XIGUAjuice/MyHoloCubic/Simulator/base_face.png

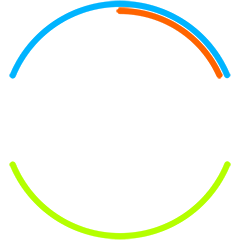
Simulator/base_face.png
