XIGUAjuice/MyHoloCubic/Simulator/smart_config.png

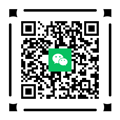
Simulator/smart_config.png
