XIGUAjuice/MyHoloCubic/Sources/pngs/1baitianqing.png

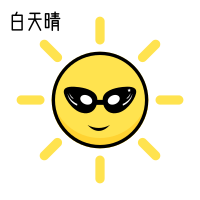
Sources/pngs/1baitianqing.png
