XIGUAjuice/MyHoloCubic/Sources/pngs/2yejianqing.png

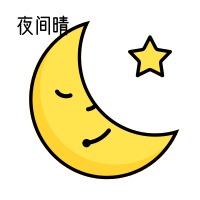
Sources/pngs/2yejianqing.png
