XIGUAjuice/MyHoloCubic/Sources/pngs/3qingtianduoyun.png

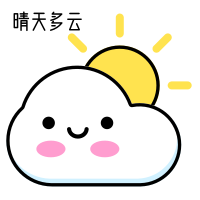
Sources/pngs/3qingtianduoyun.png
