XIGUAjuice/MyHoloCubic/Sources/pngs/4yewanduoyun.png

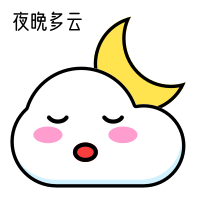
Sources/pngs/4yewanduoyun.png
