XIGUAjuice/MyHoloCubic/Sources/pngs/5yin.png

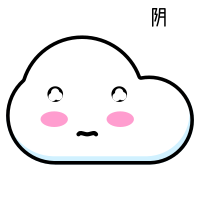
Sources/pngs/5yin.png
