XIGUAjuice/MyHoloCubic/Sources/pngs/6baitianzhenyu.png

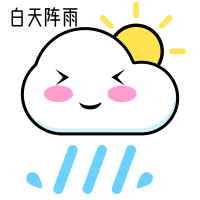
Sources/pngs/6baitianzhenyu.png
