XIGUAjuice/MyHoloCubic/Sources/pngs/7yewanzhenyu.png

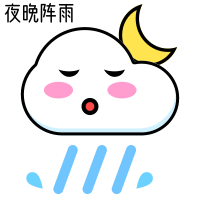
Sources/pngs/7yewanzhenyu.png
