XIGUAjuice/MyHoloCubic/Sources/pngs/10yujiaxue.png

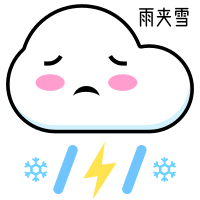
Sources/pngs/10yujiaxue.png
