XIGUAjuice/MyHoloCubic/Sources/pngs/11xiaoyu.png

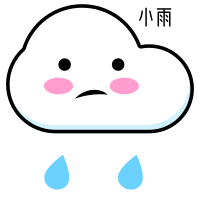
Sources/pngs/11xiaoyu.png
