XIGUAjuice/MyHoloCubic/Sources/pngs/12zhongyu.png

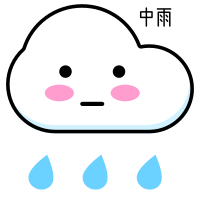
Sources/pngs/12zhongyu.png
