XIGUAjuice/MyHoloCubic/Sources/pngs/15dabaoyu.png

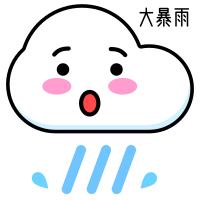
Sources/pngs/15dabaoyu.png
