XIGUAjuice/MyHoloCubic/Sources/pngs/16tedabaoyu.png

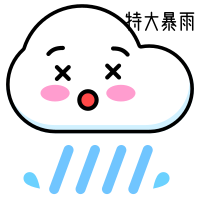
Sources/pngs/16tedabaoyu.png
