XIGUAjuice/MyHoloCubic/Sources/pngs/17qingtianzhenxue.png

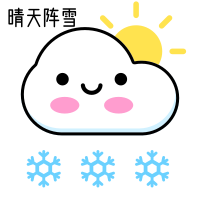
Sources/pngs/17qingtianzhenxue.png
