XIGUAjuice/MyHoloCubic/Sources/pngs/18yejianzhenxue.png

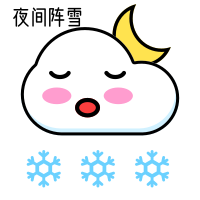
Sources/pngs/18yejianzhenxue.png
