XIGUAjuice/MyHoloCubic/Sources/pngs/19xiaoxue.png

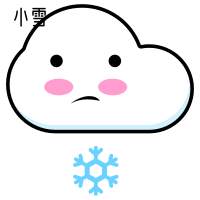
Sources/pngs/19xiaoxue.png
