XIGUAjuice/MyHoloCubic/Sources/pngs/20zhongxue.png

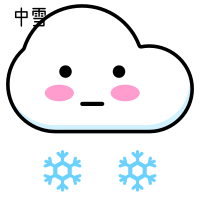
Sources/pngs/20zhongxue.png
