XIGUAjuice/MyHoloCubic/Sources/pngs/21daxue.png

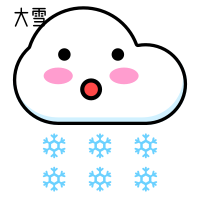
Sources/pngs/21daxue.png
