XIGUAjuice/MyHoloCubic/Sources/pngs/22baoxue.png

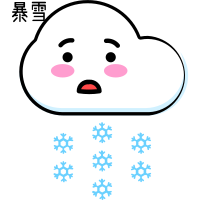
Sources/pngs/22baoxue.png
