XIGUAjuice/MyHoloCubic/Sources/pngs/24yejianwu.png

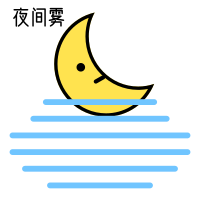
Sources/pngs/24yejianwu.png
