XIGUAjuice/MyHoloCubic/Sources/pngs/29wumai.png

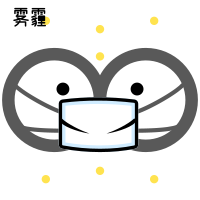
Sources/pngs/29wumai.png
