XIGUAjuice/MyHoloCubic/Sources/pngs/31reqiwengao.png

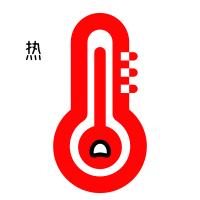
Sources/pngs/31reqiwengao.png
