XIGUAjuice/MyHoloCubic/Sources/pngs/32lengqiwendi.png

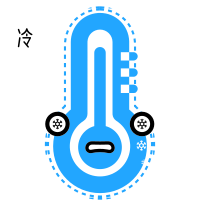
Sources/pngs/32lengqiwendi.png
