XIGUAjuice/MyHoloCubic/Sources/pngs_small_size/smart_config.png

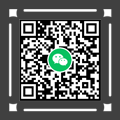
Sources/pngs_small_size/smart_config.png
