XIGUAjuice/MyHoloCubic/Simulator/png_decoder_test.c

#include "lvgl.h"

const uint8_t png_decoder_test_map[] = {
  0x89, 0x50, 0x4e, 0x47, 0x0d, 0x0a, 0x1a, 0x0a, 0x00, 0x00, 0x00, 0x0d, 0x49, 0x48, 0x44, 0x52,
  0x00, 0x00, 0x00, 0xc8, 0x00, 0x00, 0x00, 0x96, 0x08, 0x06, 0x00, 0x00, 0x00, 0x9b, 0xdc, 0xc7,
  0x19, 0x00, 0x00, 0x00, 0x06, 0x62, 0x4b, 0x47, 0x44, 0x00, 0xff, 0x00, 0xff, 0x00, 0xff, 0xa0,
  0xbd, 0xa7, 0x93, 0x00, 0x00, 0x00, 0x09, 0x70, 0x48, 0x59, 0x73, 0x00, 0x00, 0x0b, 0x13, 0x00,
  0x00, 0x0b, 0x13, 0x01, 0x00, 0x9a, 0x9c, 0x18, 0x00, 0x00, 0x00, 0x07, 0x74, 0x49, 0x4d, 0x45,
  0x07, 0xe2, 0x08, 0x1a, 0x12, 0x00, 0x07, 0x19, 0x4a, 0x0e, 0xae, 0x00, 0x00, 0x00, 0x1d, 0x69,
  0x54, 0x58, 0x74, 0x43, 0x6f, 0x6d, 0x6d, 0x65, 0x6e, 0x74, 0x00, 0x00, 0x00, 0x00, 0x00, 0x43,
  0x72, 0x65, 0x61, 0x74, 0x65, 0x64, 0x20, 0x77, 0x69, 0x74, 0x68, 0x20, 0x47, 0x49, 0x4d, 0x50,
  0x64, 0x2e, 0x65, 0x07, 0x00, 0x00, 0x20, 0x00, 0x49, 0x44, 0x41, 0x54, 0x78, 0xda, 0xec, 0xdd,
  0x79, 0xb4, 0xe5, 0xd7, 0x75, 0x17, 0xf8, 0xcf, 0xf9, 0x0d, 0x77, 0x7c, 0x53, 0xbd, 0x7a, 0x35,
  0x97, 0xa4, 0x2a, 0x95, 0x54, 0x9a, 0x6c, 0x79, 0x90, 0x12, 0xcb, 0x53, 0x8c, 0x1d, 0x03, 0x26,
  0x09, 0x26, 0x03, 0xa4, 0x93, 0x95, 0x0e, 0x43, 0x08, 0xd0, 0x9d, 0xa4, 0xd3, 0x84, 0xb1, 0x59,
  0xc0, 0x6a, 0xd6, 0xea, 0xd0, 0x8b, 0x0c, 0x74, 0x08, 0x1d, 0x12, 0x9a, 0x10, 0x02, 0x04, 0x16,
  0x8b, 0xd0, 0xed, 0x0e, 0x24, 0x24, 0x21, 0xc4, 0x4e, 0x82, 0x9d, 0x78, 0xb6, 0x2c, 0x5b, 0xb2,
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
  0xa0, 0x62, 0x1d, 0xc3, 0x9c, 0x69, 0xc6, 0xac, 0x4b, 0x2f, 0xa7, 0x5d, 0x30, 0xce, 0x92, 0x61,
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
};

lv_img_dsc_t png_decoder_test = {
  .header.always_zero = 0,
  .header.w = 200,
  .header.h = 150,
  .data_size = 20869,
  .header.cf = LV_IMG_CF_RAW_ALPHA,
  .data = png_decoder_test_map,
};
