XIGUAjuice/MyHoloCubic/Simulator/src/alphabet.c

/*******************************************************************************
 * Size: 15 px
 * Bpp: 4
 * Opts: 
 ******************************************************************************/

#ifdef LV_LVGL_H_INCLUDE_SIMPLE
#include "lvgl.h"
#else
#include "lvgl/lvgl.h"
#endif

#ifndef ALPHABET
#define ALPHABET 1
#endif

#if ALPHABET

/*-----------------
 *    BITMAPS
 *----------------*/

/*Store the image of the glyphs*/
static LV_ATTRIBUTE_LARGE_CONST const uint8_t glyph_bitmap[] = {
    /* U+0020 " " */

    /* U+0021 "!" */
    0x4b, 0x4e, 0x6d, 0x6d, 0x7c, 0x7d, 0x9b, 0x7a,
    0x0, 0x29, 0x5b, 0x0,

    /* U+0022 "\"" */
    0x10, 0x0, 0xa7, 0x68, 0xa6, 0x6c, 0x88, 0x8c,
    0x21, 0x45,

    /* U+0023 "#" */
    0x0, 0x0, 0x6b, 0xa, 0x60, 0x0, 0x0, 0xc8,
    0xe, 0x60, 0x0, 0x0, 0xf5, 0x2f, 0x20, 0x2,
    0xbd, 0xfd, 0xef, 0xda, 0x1, 0x6b, 0xd6, 0xcd,
    0x54, 0x0, 0xa, 0x90, 0xb8, 0x0, 0x0, 0xe,
    0x70, 0xea, 0x70, 0x3e, 0xdf, 0xdc, 0xfb, 0xe2,
    0x0, 0x6e, 0x5, 0xf0, 0x0, 0x0, 0x9a, 0x8,
    0xc0, 0x0, 0x0, 0x96, 0x6, 0x80, 0x0,

    /* U+0024 "$" */
    0x0, 0x4, 0xb0, 0x0, 0x0, 0x3c, 0xfa, 0x0,
    0x4, 0xfa, 0x8e, 0xd0, 0xa, 0xa0, 0x3, 0xf1,
    0x7, 0xd0, 0x1, 0xb0, 0x1, 0xdb, 0x10, 0x0,
    0x0, 0x1b, 0xf9, 0x0, 0x4, 0x0, 0x3d, 0xb0,
    0xe, 0x90, 0x5, 0xf0, 0x4, 0xfc, 0x8e, 0xb0,
    0x0, 0xbf, 0xf9, 0x10, 0x0, 0xd, 0x30, 0x0,

    /* U+0025 "%" */
    0x4, 0xef, 0x80, 0x0, 0x0, 0x0, 0xe8, 0x4e,
    0x41, 0xa0, 0x0, 0xf, 0x0, 0x99, 0x6c, 0x0,
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
    0x5, 0x30, 0x0, 0x0,

    /* U+007A "z" */
    0x0, 0x0, 0x0, 0x82, 0xb, 0xbb, 0xbe, 0xc2,
    0x0, 0x0, 0x5c, 0x10, 0x0, 0x6, 0xe1, 0x0,
    0x0, 0x4f, 0x40, 0x0, 0x3, 0xf6, 0x0, 0x0,
    0xe, 0xc5, 0x54, 0x40, 0x5f, 0xff, 0xff, 0xe2,
    0x0, 0x0, 0x0, 0x0,

    /* U+007B "{" */
    0x0, 0x1d, 0x30, 0x8, 0xc0, 0x1, 0xf3, 0x0,
    0x3f, 0x0, 0x4, 0xc0, 0x2, 0xd8, 0x0, 0x6f,
    0x40, 0x0, 0x7c, 0x0, 0x1, 0xf1, 0x0, 0xd,
    0x40, 0x0, 0x99, 0x0, 0x2, 0xe9, 0x0, 0x0,
    0x0,

    /* U+007C "|" */
    0x1e, 0x1, 0xf2, 0x2f, 0x13, 0xf1, 0x4f, 0x14,
    0xf0, 0x4f, 0x5, 0xf0, 0x5f, 0x4, 0xf0, 0x4f,
    0x5, 0xe0, 0x5e, 0x0, 0x30,

    /* U+007D "}" */
    0xbc, 0x10, 0x0, 0xbb, 0x0, 0x2, 0xf0, 0x0,
    0xf, 0x10, 0x0, 0xc5, 0x0, 0x7, 0xe4, 0x0,
    0x4f, 0x70, 0xc, 0x80, 0x1, 0xf2, 0x0, 0x3e,
    0x0, 0x9, 0x90, 0x9, 0xd2, 0x0, 0x0, 0x0,
    0x0,

    /* U+007E "~" */
    0x0, 0x0, 0x0, 0x0, 0x0, 0x2, 0xff, 0xf6,
    0x5, 0xf0, 0xc, 0xa3, 0x6e, 0xef, 0x70, 0x3,
    0x0, 0x0, 0x31, 0x0
};


/*---------------------
 *  GLYPH DESCRIPTION
 *--------------------*/

static const lv_font_fmt_txt_glyph_dsc_t glyph_dsc[] = {
    {.bitmap_index = 0, .adv_w = 0, .box_w = 0, .box_h = 0, .ofs_x = 0, .ofs_y = 0} /* id = 0 reserved */,
    {.bitmap_index = 0, .adv_w = 52, .box_w = 0, .box_h = 0, .ofs_x = 0, .ofs_y = 0},
    {.bitmap_index = 0, .adv_w = 69, .box_w = 2, .box_h = 12, .ofs_x = 1, .ofs_y = -1},
    {.bitmap_index = 12, .adv_w = 97, .box_w = 4, .box_h = 5, .ofs_x = 1, .ofs_y = 7},
    {.bitmap_index = 22, .adv_w = 150, .box_w = 10, .box_h = 11, .ofs_x = -1, .ofs_y = 0},
    {.bitmap_index = 77, .adv_w = 130, .box_w = 8, .box_h = 12, .ofs_x = 0, .ofs_y = -1},
    {.bitmap_index = 125, .adv_w = 177, .box_w = 11, .box_h = 12, .ofs_x = 0, .ofs_y = -1},
    {.bitmap_index = 191, .adv_w = 150, .box_w = 9, .box_h = 11, .ofs_x = 0, .ofs_y = 0},
    {.bitmap_index = 241, .adv_w = 48, .box_w = 3, .box_h = 4, .ofs_x = 0, .ofs_y = 7},
    {.bitmap_index = 247, .adv_w = 80, .box_w = 4, .box_h = 14, .ofs_x = 1, .ofs_y = -3},
    {.bitmap_index = 275, .adv_w = 81, .box_w = 5, .box_h = 14, .ofs_x = -1, .ofs_y = -3},
    {.bitmap_index = 310, .adv_w = 111, .box_w = 7, .box_h = 6, .ofs_x = 0, .ofs_y = 5},
    {.bitmap_index = 331, .adv_w = 136, .box_w = 10, .box_h = 9, .ofs_x = -1, .ofs_y = 0},
    {.bitmap_index = 376, .adv_w = 61, .box_w = 3, .box_h = 4, .ofs_x = 0, .ofs_y = -2},
    {.bitmap_index = 382, .adv_w = 102, .box_w = 6, .box_h = 3, .ofs_x = 0, .ofs_y = 3},
    {.bitmap_index = 391, .adv_w = 53, .box_w = 3, .box_h = 2, .ofs_x = 0, .ofs_y = 0},
    {.bitmap_index = 394, .adv_w = 86, .box_w = 5, .box_h = 12, .ofs_x = 0, .ofs_y = -1},
    {.bitmap_index = 424, .adv_w = 164, .box_w = 10, .box_h = 11, .ofs_x = 0, .ofs_y = 0},
    {.bitmap_index = 479, .adv_w = 94, .box_w = 5, .box_h = 11, .ofs_x = 0, .ofs_y = 0},
    {.bitmap_index = 507, .adv_w = 134, .box_w = 8, .box_h = 12, .ofs_x = 0, .ofs_y = -1},
    {.bitmap_index = 555, .adv_w = 134, .box_w = 8, .box_h = 11, .ofs_x = 0, .ofs_y = 0},
    {.bitmap_index = 599, .adv_w = 139, .box_w = 9, .box_h = 11, .ofs_x = 0, .ofs_y = 0},
    {.bitmap_index = 649, .adv_w = 130, .box_w = 8, .box_h = 11, .ofs_x = 0, .ofs_y = 0},
    {.bitmap_index = 693, .adv_w = 140, .box_w = 8, .box_h = 12, .ofs_x = 0, .ofs_y = 0},
    {.bitmap_index = 741, .adv_w = 127, .box_w = 8, .box_h = 11, .ofs_x = 0, .ofs_y = 0},
    {.bitmap_index = 785, .adv_w = 121, .box_w = 8, .box_h = 13, .ofs_x = 0, .ofs_y = -1},
    {.bitmap_index = 837, .adv_w = 124, .box_w = 7, .box_h = 11, .ofs_x = 0, .ofs_y = 0},
    {.bitmap_index = 876, .adv_w = 64, .box_w = 3, .box_h = 7, .ofs_x = 0, .ofs_y = 0},
    {.bitmap_index = 887, .adv_w = 67, .box_w = 3, .box_h = 8, .ofs_x = 0, .ofs_y = -1},
    {.bitmap_index = 899, .adv_w = 136, .box_w = 8, .box_h = 8, .ofs_x = 0, .ofs_y = 0},
    {.bitmap_index = 931, .adv_w = 143, .box_w = 7, .box_h = 6, .ofs_x = 1, .ofs_y = 1},
    {.bitmap_index = 952, .adv_w = 131, .box_w = 8, .box_h = 7, .ofs_x = 0, .ofs_y = 1},
    {.bitmap_index = 980, .adv_w = 106, .box_w = 6, .box_h = 11, .ofs_x = 0, .ofs_y = 0},
    {.bitmap_index = 1013, .adv_w = 191, .box_w = 11, .box_h = 13, .ofs_x = 0, .ofs_y = -2},
    {.bitmap_index = 1085, .adv_w = 156, .box_w = 10, .box_h = 11, .ofs_x = 0, .ofs_y = 0},
    {.bitmap_index = 1140, .adv_w = 136, .box_w = 8, .box_h = 11, .ofs_x = 0, .ofs_y = 0},
    {.bitmap_index = 1184, .adv_w = 148, .box_w = 9, .box_h = 13, .ofs_x = 0, .ofs_y = -1},
    {.bitmap_index = 1243, .adv_w = 150, .box_w = 8, .box_h = 11, .ofs_x = 1, .ofs_y = 0},
    {.bitmap_index = 1287, .adv_w = 125, .box_w = 8, .box_h = 11, .ofs_x = 0, .ofs_y = 0},
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
    {.bitmap_index = 3143, .adv_w = 121, .box_w = 7, .box_h = 9, .ofs_x = 0, .ofs_y = -1},
    {.bitmap_index = 3175, .adv_w = 108, .box_w = 8, .box_h = 8, .ofs_x = -1, .ofs_y = 0},
    {.bitmap_index = 3207, .adv_w = 162, .box_w = 10, .box_h = 8, .ofs_x = 0, .ofs_y = 0},
    {.bitmap_index = 3247, .adv_w = 120, .box_w = 7, .box_h = 8, .ofs_x = 0, .ofs_y = 0},
    {.bitmap_index = 3275, .adv_w = 102, .box_w = 8, .box_h = 11, .ofs_x = -1, .ofs_y = -3},
    {.bitmap_index = 3319, .adv_w = 125, .box_w = 8, .box_h = 9, .ofs_x = 0, .ofs_y = -1},
    {.bitmap_index = 3355, .adv_w = 80, .box_w = 5, .box_h = 13, .ofs_x = 0, .ofs_y = -2},
    {.bitmap_index = 3388, .adv_w = 75, .box_w = 3, .box_h = 14, .ofs_x = 1, .ofs_y = -3},
    {.bitmap_index = 3409, .adv_w = 93, .box_w = 5, .box_h = 13, .ofs_x = 0, .ofs_y = -2},
    {.bitmap_index = 3442, .adv_w = 157, .box_w = 10, .box_h = 4, .ofs_x = 0, .ofs_y = 3}
};

/*---------------------
 *  CHARACTER MAPPING
 *--------------------*/



/*Collect the unicode lists and glyph_id offsets*/
static const lv_font_fmt_txt_cmap_t cmaps[] =
{
    {
        .range_start = 32, .range_length = 95, .glyph_id_start = 1,
        .unicode_list = NULL, .glyph_id_ofs_list = NULL, .list_length = 0, .type = LV_FONT_FMT_TXT_CMAP_FORMAT0_TINY
    }
};

/*-----------------
 *    KERNING
 *----------------*/


/*Pair left and right glyphs for kerning*/
static const uint8_t kern_pair_glyph_ids[] =
{
    14, 49,
    15, 41,
    15, 46,
    15, 47,
    15, 49,
    15, 51,
    15, 53,
    15, 54,
    15, 55,
    15, 58,
    19, 20,
    23, 24,
    34, 8,
    34, 35,
    34, 53,
    34, 55,
    34, 56,
    34, 78,
    34, 86,
    34, 87,
    34, 88,
    34, 90,
    34, 91,
    36, 37,
    36, 48,
    37, 86,
    38, 47,
    38, 89,
    39, 40,
    39, 66,
    39, 70,
    39, 80,
    40, 41,
    40, 77,
    41, 15,
    41, 70,
    42, 68,
    43, 15,
    45, 53,
    46, 15,
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
};

/* Kerning between the respective left and right glyphs
 * 4.4 format which needs to scaled with `kern_scale`*/
static const int8_t kern_pair_values[] =
{
    -5, -7, -10, -10, -7, -7, -31, -12,
    -29, -14, -7, -2, -18, -7, -19, -31,
    -14, -5, -10, -14, -7, -10, -2, -3,
    -10, -5, 5, -12, -10, -14, -7, -12,
    -5, -2, -7, -10, -1, -12, -19, -7,
    -46, -26, -7, -10, -5, -17, -7, -14,
    -14, -14, -14, -7, -14, -7, -11, -10,
    -7, -12, -7, -7, -7, -7, -7, -7,
    -12, -4, -5, -18, 5, -14, -22, -4,
    -10, -17, -14, -26, -12, -5, -7, -22,
    -7, -14, -12, 5, -7, -5, -5, -10,
    -7, -5, -14, -10, -7, -7, -5, -14,
    -5, 2, -2, -5, 0, -12, -14, -7,
    -2, -5, -10, -14, -17, -14, -10, -7,
    -5, 2, -10, -10, 2, 5, -6, -2,
    7, 5, -5, -10, -14, -10, -3, -7,
    -10, 5, -5, -2, -5, -11, -10, 0,
    -7, -2, 2, -2, -2, -10, -10, 2,
    -10, 7, 19, -17, -14, -7, -5, -5,
    -5, -12, -11, -10, -5, -7, -11, -5,
    -7, -7, -5, -22, -7, -7, -7, -5,
    -5, -7, -2
};

/*Collect the kern pair's data in one place*/
static const lv_font_fmt_txt_kern_pair_t kern_pairs =
{
    .glyph_ids = kern_pair_glyph_ids,
    .values = kern_pair_values,
    .pair_cnt = 171,
    .glyph_ids_size = 0
};

/*--------------------
 *  ALL CUSTOM DATA
 *--------------------*/

#if LV_VERSION_CHECK(8, 0, 0)
/*Store all the custom data of the font*/
static  lv_font_fmt_txt_glyph_cache_t cache;
static const lv_font_fmt_txt_dsc_t font_dsc = {
#else
static lv_font_fmt_txt_dsc_t font_dsc = {
#endif
    .glyph_bitmap = glyph_bitmap,
    .glyph_dsc = glyph_dsc,
    .cmaps = cmaps,
    .kern_dsc = &kern_pairs,
    .kern_scale = 16,
    .cmap_num = 1,
    .bpp = 4,
    .kern_classes = 0,
    .bitmap_format = 0,
#if LV_VERSION_CHECK(8, 0, 0)
    .cache = &cache
#endif
};


/*-----------------
 *  PUBLIC FONT
 *----------------*/

/*Initialize a public general font descriptor*/
#if LV_VERSION_CHECK(8, 0, 0)
const lv_font_t alphabet = {
#else
lv_font_t alphabet = {
#endif
    .get_glyph_dsc = lv_font_get_glyph_dsc_fmt_txt,    /*Function pointer to get glyph's data*/
    .get_glyph_bitmap = lv_font_get_bitmap_fmt_txt,    /*Function pointer to get glyph's bitmap*/
    .line_height = 15,          /*The maximum line height required by the font*/
    .base_line = 3,             /*Baseline measured from the bottom of the line*/
#if !(LVGL_VERSION_MAJOR == 6 && LVGL_VERSION_MINOR == 0)
    .subpx = LV_FONT_SUBPX_NONE,
#endif
#if LV_VERSION_CHECK(7, 4, 0)
    .underline_position = -1,
    .underline_thickness = 1,
#endif
    .dsc = &font_dsc           /*The custom font data. Will be accessed by `get_glyph_bitmap/dsc` */
};



#endif /*#if ALPHABET*/
