XIGUAjuice/MyHoloCubic/Simulator/src/digital.c

/*******************************************************************************
 * Size: 75 px
 * Bpp: 1
 * Opts: 
 ******************************************************************************/

#ifdef LV_LVGL_H_INCLUDE_SIMPLE
#include "lvgl.h"
#else
#include "lvgl/lvgl.h"
#endif

#ifndef DIGITAL
#define DIGITAL 1
#endif

#if DIGITAL

/*-----------------
 *    BITMAPS
 *----------------*/

/*Store the image of the glyphs*/
static LV_ATTRIBUTE_LARGE_CONST const uint8_t glyph_bitmap[] = {
    /* U+0020 " " */
    0x0,

    /* U+0021 "!" */
    0x3e, 0x3f, 0x9f, 0xcf, 0xe7, 0xf3, 0xf9, 0xfc,
    0xfe, 0x7f, 0x3f, 0x9f, 0xcf, 0xe7, 0xf3, 0xf9,
    0xfc, 0xfe, 0x7f, 0x3f, 0x9f, 0xcf, 0xe7, 0xf3,
    0xf9, 0xfc, 0xfe, 0x7f, 0x3f, 0x9f, 0xcf, 0xe7,
    0xf3, 0xf9, 0xfc, 0xfe, 0x7f, 0x3f, 0x9f, 0xcf,
    0xe7, 0xf3, 0xf9, 0xfc, 0xfe, 0x7f, 0x3f, 0x9f,
    0xcf, 0xe7, 0xf3, 0xf9, 0xfc, 0xfe, 0x7f, 0x3f,
    0x9f, 0xcf, 0xe7, 0xf3, 0xf9, 0xfc, 0xfe, 0x3e,
    0x0, 0x0, 0x0, 0x1, 0xc1, 0xf1, 0xfd, 0xff,
    0xff, 0xff, 0xdf, 0xc7, 0xc1, 0xc0,

    /* U+0022 "\"" */
    0x70, 0x77, 0xc7, 0xfe, 0x3f, 0xf1, 0xff, 0x8f,
    0xf8, 0x7f, 0xc3, 0xde, 0x1e, 0xf0, 0xf7, 0x83,
    0x9c, 0x1c, 0xe0, 0xe6, 0x6, 0x0,

    /* U+0023 "#" */
    0x0, 0x1, 0xf0, 0x0, 0xf8, 0x0, 0x0, 0x7f,
    0x0, 0x3f, 0x80, 0x0, 0xf, 0xe0, 0xf, 0xf0,
    0x0, 0x1, 0xfc, 0x1, 0xfe, 0x0, 0x0, 0x7f,
    0x80, 0x3f, 0xc0, 0x0, 0xf, 0xf0, 0x7, 0xf8,
    0x0, 0x1, 0xfe, 0x0, 0xfe, 0x0, 0x0, 0x3f,
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
    0x1, 0xfc, 0x0, 0xfe, 0x0, 0x7f, 0x0, 0x3f,
    0x80, 0x1f, 0xc0, 0xf, 0xe0, 0x7, 0xf0, 0x3,
    0xf8, 0x1, 0xfc, 0x0, 0xfe, 0x0, 0xff, 0x0,
    0x7f, 0x0, 0x7f, 0x80, 0x7f, 0x80, 0x7f, 0x80,
    0x7f, 0x80, 0x3f, 0x80, 0x3f, 0xc0, 0x1f, 0xc0,
    0x7, 0xc0, 0x0,

    /* U+007E "~" */
    0x3, 0xc0, 0x0, 0x0, 0xfe, 0x0, 0x0, 0x1f,
    0xf8, 0x0, 0x7, 0xff, 0xc0, 0x0, 0xff, 0xff,
    0x0, 0x6f, 0xff, 0xf8, 0x1f, 0xff, 0xff, 0xe3,
    0xff, 0xff, 0xff, 0xff, 0xfc, 0x7f, 0xff, 0xff,
    0x1, 0xff, 0xff, 0x60, 0xf, 0xff, 0xe0, 0x0,
    0x3f, 0xfe, 0x0, 0x1, 0xff, 0x80, 0x0, 0x7,
    0xf0, 0x0, 0x0, 0x3c, 0x0
};


/*---------------------
 *  GLYPH DESCRIPTION
 *--------------------*/

static const lv_font_fmt_txt_glyph_dsc_t glyph_dsc[] = {
    {.bitmap_index = 0, .adv_w = 0, .box_w = 0, .box_h = 0, .ofs_x = 0, .ofs_y = 0} /* id = 0 reserved */,
    {.bitmap_index = 0, .adv_w = 216, .box_w = 1, .box_h = 1, .ofs_x = 0, .ofs_y = 0},
    {.bitmap_index = 1, .adv_w = 235, .box_w = 9, .box_h = 69, .ofs_x = 3, .ofs_y = -8},
    {.bitmap_index = 79, .adv_w = 260, .box_w = 13, .box_h = 13, .ofs_x = 2, .ofs_y = 45},
    {.bitmap_index = 101, .adv_w = 709, .box_w = 43, .box_h = 69, .ofs_x = 2, .ofs_y = -7},
    {.bitmap_index = 472, .adv_w = 595, .box_w = 31, .box_h = 69, .ofs_x = 4, .ofs_y = -7},
    {.bitmap_index = 740, .adv_w = 616, .box_w = 33, .box_h = 69, .ofs_x = 1, .ofs_y = -7},
    {.bitmap_index = 1025, .adv_w = 587, .box_w = 31, .box_h = 69, .ofs_x = 4, .ofs_y = -7},
    {.bitmap_index = 1293, .adv_w = 128, .box_w = 6, .box_h = 13, .ofs_x = 1, .ofs_y = 45},
    {.bitmap_index = 1303, .adv_w = 367, .box_w = 16, .box_h = 69, .ofs_x = 4, .ofs_y = -7},
    {.bitmap_index = 1441, .adv_w = 368, .box_w = 15, .box_h = 69, .ofs_x = 3, .ofs_y = -7},
    {.bitmap_index = 1571, .adv_w = 497, .box_w = 28, .box_h = 33, .ofs_x = 1, .ofs_y = 13},
    {.bitmap_index = 1687, .adv_w = 766, .box_w = 42, .box_h = 45, .ofs_x = 3, .ofs_y = 7},
    {.bitmap_index = 1924, .adv_w = 238, .box_w = 9, .box_h = 15, .ofs_x = 3, .ofs_y = -7},
    {.bitmap_index = 1941, .adv_w = 390, .box_w = 20, .box_h = 7, .ofs_x = 2, .ofs_y = 22},
    {.bitmap_index = 1959, .adv_w = 217, .box_w = 7, .box_h = 9, .ofs_x = 3, .ofs_y = -7},
    {.bitmap_index = 1967, .adv_w = 398, .box_w = 19, .box_h = 69, .ofs_x = 4, .ofs_y = -7},
    {.bitmap_index = 2131, .adv_w = 610, .box_w = 31, .box_h = 55, .ofs_x = 4, .ofs_y = -1},
    {.bitmap_index = 2345, .adv_w = 317, .box_w = 17, .box_h = 55, .ofs_x = 1, .ofs_y = -1},
    {.bitmap_index = 2462, .adv_w = 608, .box_w = 31, .box_h = 55, .ofs_x = 4, .ofs_y = -1},
    {.bitmap_index = 2676, .adv_w = 598, .box_w = 31, .box_h = 55, .ofs_x = 2, .ofs_y = -1},
    {.bitmap_index = 2890, .adv_w = 599, .box_w = 31, .box_h = 55, .ofs_x = 3, .ofs_y = -1},
    {.bitmap_index = 3104, .adv_w = 610, .box_w = 31, .box_h = 55, .ofs_x = 4, .ofs_y = -1},
    {.bitmap_index = 3318, .adv_w = 610, .box_w = 31, .box_h = 55, .ofs_x = 4, .ofs_y = -1},
    {.bitmap_index = 3532, .adv_w = 461, .box_w = 28, .box_h = 55, .ofs_x = -3, .ofs_y = -1},
    {.bitmap_index = 3725, .adv_w = 611, .box_w = 31, .box_h = 55, .ofs_x = 4, .ofs_y = -1},
    {.bitmap_index = 3939, .adv_w = 610, .box_w = 31, .box_h = 55, .ofs_x = 4, .ofs_y = -1},
    {.bitmap_index = 4153, .adv_w = 217, .box_w = 7, .box_h = 37, .ofs_x = 3, .ofs_y = 11},
    {.bitmap_index = 4186, .adv_w = 286, .box_w = 9, .box_h = 44, .ofs_x = 4, .ofs_y = 4},
    {.bitmap_index = 4236, .adv_w = 667, .box_w = 36, .box_h = 65, .ofs_x = 3, .ofs_y = -6},
    {.bitmap_index = 4529, .adv_w = 766, .box_w = 42, .box_h = 28, .ofs_x = 3, .ofs_y = 17},
    {.bitmap_index = 4676, .adv_w = 668, .box_w = 36, .box_h = 65, .ofs_x = 3, .ofs_y = -6},
    {.bitmap_index = 4969, .adv_w = 412, .box_w = 26, .box_h = 62, .ofs_x = -1, .ofs_y = -1},
    {.bitmap_index = 5171, .adv_w = 817, .box_w = 44, .box_h = 55, .ofs_x = 4, .ofs_y = -1},
    {.bitmap_index = 5474, .adv_w = 637, .box_w = 35, .box_h = 55, .ofs_x = 2, .ofs_y = -1},
    {.bitmap_index = 5715, .adv_w = 594, .box_w = 30, .box_h = 55, .ofs_x = 4, .ofs_y = -1},
    {.bitmap_index = 5922, .adv_w = 595, .box_w = 30, .box_h = 55, .ofs_x = 4, .ofs_y = -1},
    {.bitmap_index = 6129, .adv_w = 595, .box_w = 30, .box_h = 55, .ofs_x = 4, .ofs_y = -1},
    {.bitmap_index = 6336, .adv_w = 582, .box_w = 30, .box_h = 55, .ofs_x = 4, .ofs_y = -1},
    {.bitmap_index = 6543, .adv_w = 582, .box_w = 30, .box_h = 55, .ofs_x = 4, .ofs_y = -1},
    {.bitmap_index = 6750, .adv_w = 595, .box_w = 30, .box_h = 55, .ofs_x = 4, .ofs_y = -1},
    {.bitmap_index = 6957, .adv_w = 595, .box_w = 30, .box_h = 55, .ofs_x = 4, .ofs_y = -1},
    {.bitmap_index = 7164, .adv_w = 326, .box_w = 17, .box_h = 55, .ofs_x = 1, .ofs_y = -1},
    {.bitmap_index = 7281, .adv_w = 493, .box_w = 23, .box_h = 55, .ofs_x = 4, .ofs_y = -1},
    {.bitmap_index = 7440, .adv_w = 583, .box_w = 30, .box_h = 55, .ofs_x = 4, .ofs_y = -1},
    {.bitmap_index = 7647, .adv_w = 582, .box_w = 30, .box_h = 55, .ofs_x = 4, .ofs_y = -1},
    {.bitmap_index = 7854, .adv_w = 740, .box_w = 39, .box_h = 55, .ofs_x = 4, .ofs_y = -1},
    {.bitmap_index = 8123, .adv_w = 606, .box_w = 30, .box_h = 55, .ofs_x = 4, .ofs_y = -1},
    {.bitmap_index = 8330, .adv_w = 595, .box_w = 30, .box_h = 55, .ofs_x = 4, .ofs_y = -1},
    {.bitmap_index = 8537, .adv_w = 583, .box_w = 30, .box_h = 55, .ofs_x = 4, .ofs_y = -1},
    {.bitmap_index = 8744, .adv_w = 593, .box_w = 30, .box_h = 61, .ofs_x = 4, .ofs_y = -7},
    {.bitmap_index = 8973, .adv_w = 582, .box_w = 30, .box_h = 55, .ofs_x = 4, .ofs_y = -1},
    {.bitmap_index = 9180, .adv_w = 595, .box_w = 30, .box_h = 56, .ofs_x = 4, .ofs_y = -1},
    {.bitmap_index = 9390, .adv_w = 451, .box_w = 30, .box_h = 55, .ofs_x = -1, .ofs_y = -1},
    {.bitmap_index = 9597, .adv_w = 595, .box_w = 30, .box_h = 55, .ofs_x = 4, .ofs_y = -1},
    {.bitmap_index = 9804, .adv_w = 565, .box_w = 35, .box_h = 55, .ofs_x = 0, .ofs_y = -1},
    {.bitmap_index = 10045, .adv_w = 692, .box_w = 41, .box_h = 55, .ofs_x = 1, .ofs_y = -1},
    {.bitmap_index = 10327, .adv_w = 617, .box_w = 33, .box_h = 55, .ofs_x = 3, .ofs_y = -1},
    {.bitmap_index = 10554, .adv_w = 515, .box_w = 34, .box_h = 55, .ofs_x = -1, .ofs_y = -1},
    {.bitmap_index = 10788, .adv_w = 596, .box_w = 30, .box_h = 55, .ofs_x = 4, .ofs_y = -1},
    {.bitmap_index = 10995, .adv_w = 342, .box_w = 17, .box_h = 68, .ofs_x = 4, .ofs_y = -7},
    {.bitmap_index = 11140, .adv_w = 372, .box_w = 18, .box_h = 70, .ofs_x = 1, .ofs_y = -7},
    {.bitmap_index = 11298, .adv_w = 342, .box_w = 17, .box_h = 69, .ofs_x = 0, .ofs_y = -7},
    {.bitmap_index = 11445, .adv_w = 637, .box_w = 34, .box_h = 28, .ofs_x = 3, .ofs_y = 25},
    {.bitmap_index = 11564, .adv_w = 612, .box_w = 34, .box_h = 5, .ofs_x = 2, .ofs_y = 5},
    {.bitmap_index = 11586, .adv_w = 158, .box_w = 10, .box_h = 11, .ofs_x = 0, .ofs_y = 52},
    {.bitmap_index = 11600, .adv_w = 526, .box_w = 25, .box_h = 38, .ofs_x = 4, .ofs_y = -1},
    {.bitmap_index = 11719, .adv_w = 510, .box_w = 24, .box_h = 55, .ofs_x = 4, .ofs_y = -1},
    {.bitmap_index = 11884, .adv_w = 486, .box_w = 25, .box_h = 38, .ofs_x = 4, .ofs_y = -1},
    {.bitmap_index = 12003, .adv_w = 510, .box_w = 24, .box_h = 55, .ofs_x = 4, .ofs_y = -1},
    {.bitmap_index = 12168, .adv_w = 510, .box_w = 24, .box_h = 38, .ofs_x = 4, .ofs_y = -1},
    {.bitmap_index = 12282, .adv_w = 364, .box_w = 19, .box_h = 55, .ofs_x = 2, .ofs_y = -1},
    {.bitmap_index = 12413, .adv_w = 523, .box_w = 25, .box_h = 44, .ofs_x = 4, .ofs_y = -7},
    {.bitmap_index = 12551, .adv_w = 522, .box_w = 24, .box_h = 55, .ofs_x = 4, .ofs_y = -1},
    {.bitmap_index = 12716, .adv_w = 254, .box_w = 7, .box_h = 49, .ofs_x = 4, .ofs_y = -1},
    {.bitmap_index = 12759, .adv_w = 252, .box_w = 12, .box_h = 56, .ofs_x = -1, .ofs_y = -7},
    {.bitmap_index = 12843, .adv_w = 436, .box_w = 23, .box_h = 55, .ofs_x = 4, .ofs_y = -1},
    {.bitmap_index = 13002, .adv_w = 228, .box_w = 7, .box_h = 55, .ofs_x = 4, .ofs_y = -1},
    {.bitmap_index = 13051, .adv_w = 710, .box_w = 36, .box_h = 38, .ofs_x = 4, .ofs_y = -1},
    {.bitmap_index = 13222, .adv_w = 536, .box_w = 25, .box_h = 38, .ofs_x = 4, .ofs_y = -1},
    {.bitmap_index = 13341, .adv_w = 512, .box_w = 25, .box_h = 38, .ofs_x = 4, .ofs_y = -1},
    {.bitmap_index = 13460, .adv_w = 522, .box_w = 24, .box_h = 44, .ofs_x = 4, .ofs_y = -7},
    {.bitmap_index = 13592, .adv_w = 522, .box_w = 24, .box_h = 44, .ofs_x = 4, .ofs_y = -7},
    {.bitmap_index = 13724, .adv_w = 276, .box_w = 12, .box_h = 38, .ofs_x = 4, .ofs_y = -1},
    {.bitmap_index = 13781, .adv_w = 511, .box_w = 25, .box_h = 38, .ofs_x = 4, .ofs_y = -1},
    {.bitmap_index = 13900, .adv_w = 408, .box_w = 22, .box_h = 47, .ofs_x = 2, .ofs_y = -1},
    {.bitmap_index = 14030, .adv_w = 535, .box_w = 25, .box_h = 38, .ofs_x = 4, .ofs_y = -1},
    {.bitmap_index = 14149, .adv_w = 446, .box_w = 23, .box_h = 38, .ofs_x = 2, .ofs_y = -1},
    {.bitmap_index = 14259, .adv_w = 725, .box_w = 41, .box_h = 38, .ofs_x = 2, .ofs_y = -1},
    {.bitmap_index = 14454, .adv_w = 428, .box_w = 25, .box_h = 38, .ofs_x = 1, .ofs_y = -1},
    {.bitmap_index = 14573, .adv_w = 499, .box_w = 25, .box_h = 44, .ofs_x = 3, .ofs_y = -7},
    {.bitmap_index = 14711, .adv_w = 461, .box_w = 24, .box_h = 37, .ofs_x = 2, .ofs_y = 0},
    {.bitmap_index = 14822, .adv_w = 325, .box_w = 17, .box_h = 67, .ofs_x = 3, .ofs_y = -7},
    {.bitmap_index = 14965, .adv_w = 233, .box_w = 7, .box_h = 69, .ofs_x = 4, .ofs_y = -7},
    {.bitmap_index = 15026, .adv_w = 328, .box_w = 17, .box_h = 69, .ofs_x = 1, .ofs_y = -7},
    {.bitmap_index = 15173, .adv_w = 515, .box_w = 28, .box_h = 15, .ofs_x = 2, .ofs_y = 24}
};

/*---------------------
 *  CHARACTER MAPPING
 *--------------------*/



/*Collect the unicode lists and glyph_id offsets*/
static const lv_font_fmt_txt_cmap_t cmaps[] =
{
    {
        .range_start = 32, .range_length = 95, .glyph_id_start = 1,
        .unicode_list = NULL, .glyph_id_ofs_list = NULL, .list_length = 0, .type = LV_FONT_FMT_TXT_CMAP_FORMAT0_TINY
    }
};



/*--------------------
 *  ALL CUSTOM DATA
 *--------------------*/

#if LV_VERSION_CHECK(8, 0, 0)
/*Store all the custom data of the font*/
static  lv_font_fmt_txt_glyph_cache_t cache;
static const lv_font_fmt_txt_dsc_t font_dsc = {
#else
static lv_font_fmt_txt_dsc_t font_dsc = {
#endif
    .glyph_bitmap = glyph_bitmap,
    .glyph_dsc = glyph_dsc,
    .cmaps = cmaps,
    .kern_dsc = NULL,
    .kern_scale = 0,
    .cmap_num = 1,
    .bpp = 1,
    .kern_classes = 0,
    .bitmap_format = 0,
#if LV_VERSION_CHECK(8, 0, 0)
    .cache = &cache
#endif
};


/*-----------------
 *  PUBLIC FONT
 *----------------*/

/*Initialize a public general font descriptor*/
#if LV_VERSION_CHECK(8, 0, 0)
const lv_font_t digital = {
#else
lv_font_t digital = {
#endif
    .get_glyph_dsc = lv_font_get_glyph_dsc_fmt_txt,    /*Function pointer to get glyph's data*/
    .get_glyph_bitmap = lv_font_get_bitmap_fmt_txt,    /*Function pointer to get glyph's bitmap*/
    .line_height = 71,          /*The maximum line height required by the font*/
    .base_line = 8,             /*Baseline measured from the bottom of the line*/
#if !(LVGL_VERSION_MAJOR == 6 && LVGL_VERSION_MINOR == 0)
    .subpx = LV_FONT_SUBPX_NONE,
#endif
#if LV_VERSION_CHECK(7, 4, 0)
    .underline_position = -6,
    .underline_thickness = 4,
#endif
    .dsc = &font_dsc           /*The custom font data. Will be accessed by `get_glyph_bitmap/dsc` */
};



#endif /*#if DIGITAL*/
