XIGUAjuice/MyHoloCubic/Simulator/src/digital_medium.c

/*******************************************************************************
 * Size: 40 px
 * Bpp: 1
 * Opts: 
 ******************************************************************************/

#ifdef LV_LVGL_H_INCLUDE_SIMPLE
#include "lvgl.h"
#else
#include "lvgl/lvgl.h"
#endif

#ifndef DIGITAL_MEDIUM
#define DIGITAL_MEDIUM 1
#endif

#if DIGITAL_MEDIUM

/*-----------------
 *    BITMAPS
 *----------------*/

/*Store the image of the glyphs*/
static LV_ATTRIBUTE_LARGE_CONST const uint8_t glyph_bitmap[] = {
    /* U+0020 " " */
    0x0,

    /* U+0021 "!" */
    0xff, 0xff, 0xff, 0xff, 0xff, 0xff, 0xff, 0xff,
    0xff, 0xff, 0xff, 0xff, 0xff, 0xff, 0xff, 0xf0,
    0x6, 0xff, 0xf6,

    /* U+0022 "\"" */
    0xcf, 0x9f, 0x3e, 0x7c, 0x78, 0xb1, 0x0,

    /* U+0023 "#" */
    0x0, 0x40, 0x20, 0x3, 0xc1, 0xe0, 0x7, 0x83,
    0xc0, 0xf, 0x7, 0x80, 0x3e, 0x1f, 0x0, 0x78,
    0x3c, 0x0, 0xf0, 0x78, 0x1, 0xf0, 0xf8, 0x7f,
    0xff, 0xfe, 0xff, 0xff, 0xfd, 0xff, 0xff, 0xfb,
    0xff, 0xff, 0xf0, 0x7c, 0x3e, 0x0, 0xf0, 0x78,
    0x1, 0xe0, 0xf0, 0x3, 0xc1, 0xe0, 0xf, 0x87,
    0xc0, 0x1e, 0xf, 0x80, 0x3c, 0x1e, 0x0, 0x78,
    0x3c, 0x0, 0xf0, 0x78, 0x1, 0xe0, 0xf0, 0x7,
    0xc3, 0xe0, 0xf, 0x7, 0x80, 0x1e, 0xf, 0x0,
    0x3c, 0x1e, 0x0, 0x78, 0x7c, 0x7, 0xff, 0xff,
    0x8f, 0xff, 0xff, 0x1f, 0xff, 0xfe, 0x3f, 0xff,
    0xfc, 0x1e, 0x1f, 0x0, 0x3c, 0x1e, 0x0, 0xf8,
    0x7c, 0x1, 0xf0, 0xf0, 0x3, 0xc1, 0xe0, 0x7,
    0x83, 0xc0, 0xf, 0x7, 0x80, 0x0,

    /* U+0024 "$" */
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
    0xe0, 0xf0, 0x78, 0x3c, 0x3e, 0x1e, 0x1e, 0x1e,
    0xe, 0x0,

    /* U+007E "~" */
    0x18, 0x0, 0xfc, 0x3, 0xfc, 0x7, 0xfe, 0x7e,
    0x7f, 0xe0, 0x3f, 0xc0, 0x3f, 0x0, 0x38
};


/*---------------------
 *  GLYPH DESCRIPTION
 *--------------------*/

static const lv_font_fmt_txt_glyph_dsc_t glyph_dsc[] = {
    {.bitmap_index = 0, .adv_w = 0, .box_w = 0, .box_h = 0, .ofs_x = 0, .ofs_y = 0} /* id = 0 reserved */,
    {.bitmap_index = 0, .adv_w = 115, .box_w = 1, .box_h = 1, .ofs_x = 0, .ofs_y = 0},
    {.bitmap_index = 1, .adv_w = 125, .box_w = 4, .box_h = 38, .ofs_x = 2, .ofs_y = -4},
    {.bitmap_index = 20, .adv_w = 139, .box_w = 7, .box_h = 7, .ofs_x = 1, .ofs_y = 24},
    {.bitmap_index = 27, .adv_w = 378, .box_w = 23, .box_h = 38, .ofs_x = 1, .ofs_y = -4},
    {.bitmap_index = 137, .adv_w = 317, .box_w = 16, .box_h = 37, .ofs_x = 2, .ofs_y = -4},
    {.bitmap_index = 211, .adv_w = 328, .box_w = 18, .box_h = 38, .ofs_x = 1, .ofs_y = -4},
    {.bitmap_index = 297, .adv_w = 313, .box_w = 17, .box_h = 38, .ofs_x = 2, .ofs_y = -4},
    {.bitmap_index = 378, .adv_w = 68, .box_w = 3, .box_h = 7, .ofs_x = 1, .ofs_y = 24},
    {.bitmap_index = 381, .adv_w = 196, .box_w = 8, .box_h = 37, .ofs_x = 2, .ofs_y = -4},
    {.bitmap_index = 418, .adv_w = 196, .box_w = 8, .box_h = 37, .ofs_x = 2, .ofs_y = -4},
    {.bitmap_index = 455, .adv_w = 265, .box_w = 15, .box_h = 18, .ofs_x = 1, .ofs_y = 7},
    {.bitmap_index = 489, .adv_w = 408, .box_w = 22, .box_h = 24, .ofs_x = 2, .ofs_y = 4},
    {.bitmap_index = 555, .adv_w = 127, .box_w = 4, .box_h = 9, .ofs_x = 2, .ofs_y = -4},
    {.bitmap_index = 560, .adv_w = 208, .box_w = 11, .box_h = 4, .ofs_x = 1, .ofs_y = 12},
    {.bitmap_index = 566, .adv_w = 116, .box_w = 4, .box_h = 5, .ofs_x = 2, .ofs_y = -4},
    {.bitmap_index = 569, .adv_w = 212, .box_w = 10, .box_h = 38, .ofs_x = 2, .ofs_y = -4},
    {.bitmap_index = 617, .adv_w = 325, .box_w = 16, .box_h = 29, .ofs_x = 2, .ofs_y = 0},
    {.bitmap_index = 675, .adv_w = 169, .box_w = 9, .box_h = 29, .ofs_x = 1, .ofs_y = 0},
    {.bitmap_index = 708, .adv_w = 324, .box_w = 16, .box_h = 29, .ofs_x = 2, .ofs_y = 0},
    {.bitmap_index = 766, .adv_w = 319, .box_w = 17, .box_h = 29, .ofs_x = 1, .ofs_y = 0},
    {.bitmap_index = 828, .adv_w = 319, .box_w = 17, .box_h = 29, .ofs_x = 2, .ofs_y = 0},
    {.bitmap_index = 890, .adv_w = 325, .box_w = 16, .box_h = 29, .ofs_x = 2, .ofs_y = 0},
    {.bitmap_index = 948, .adv_w = 325, .box_w = 16, .box_h = 29, .ofs_x = 2, .ofs_y = 0},
    {.bitmap_index = 1006, .adv_w = 246, .box_w = 15, .box_h = 29, .ofs_x = -1, .ofs_y = 0},
    {.bitmap_index = 1061, .adv_w = 326, .box_w = 17, .box_h = 29, .ofs_x = 2, .ofs_y = 0},
    {.bitmap_index = 1123, .adv_w = 325, .box_w = 16, .box_h = 29, .ofs_x = 2, .ofs_y = 0},
    {.bitmap_index = 1181, .adv_w = 116, .box_w = 4, .box_h = 20, .ofs_x = 2, .ofs_y = 6},
    {.bitmap_index = 1191, .adv_w = 152, .box_w = 4, .box_h = 24, .ofs_x = 2, .ofs_y = 2},
    {.bitmap_index = 1203, .adv_w = 356, .box_w = 19, .box_h = 35, .ofs_x = 2, .ofs_y = -3},
    {.bitmap_index = 1287, .adv_w = 408, .box_w = 22, .box_h = 15, .ofs_x = 2, .ofs_y = 9},
    {.bitmap_index = 1329, .adv_w = 356, .box_w = 20, .box_h = 35, .ofs_x = 1, .ofs_y = -3},
    {.bitmap_index = 1417, .adv_w = 220, .box_w = 14, .box_h = 34, .ofs_x = 0, .ofs_y = 0},
    {.bitmap_index = 1477, .adv_w = 436, .box_w = 23, .box_h = 29, .ofs_x = 2, .ofs_y = 0},
    {.bitmap_index = 1561, .adv_w = 340, .box_w = 19, .box_h = 29, .ofs_x = 1, .ofs_y = 0},
    {.bitmap_index = 1630, .adv_w = 317, .box_w = 16, .box_h = 29, .ofs_x = 2, .ofs_y = 0},
    {.bitmap_index = 1688, .adv_w = 317, .box_w = 16, .box_h = 29, .ofs_x = 2, .ofs_y = 0},
    {.bitmap_index = 1746, .adv_w = 317, .box_w = 16, .box_h = 29, .ofs_x = 2, .ofs_y = 0},
    {.bitmap_index = 1804, .adv_w = 310, .box_w = 16, .box_h = 29, .ofs_x = 2, .ofs_y = 0},
    {.bitmap_index = 1862, .adv_w = 310, .box_w = 16, .box_h = 29, .ofs_x = 2, .ofs_y = 0},
    {.bitmap_index = 1920, .adv_w = 317, .box_w = 16, .box_h = 29, .ofs_x = 2, .ofs_y = 0},
    {.bitmap_index = 1978, .adv_w = 317, .box_w = 16, .box_h = 29, .ofs_x = 2, .ofs_y = 0},
    {.bitmap_index = 2036, .adv_w = 174, .box_w = 9, .box_h = 29, .ofs_x = 1, .ofs_y = 0},
    {.bitmap_index = 2069, .adv_w = 263, .box_w = 13, .box_h = 29, .ofs_x = 2, .ofs_y = 0},
    {.bitmap_index = 2117, .adv_w = 311, .box_w = 16, .box_h = 29, .ofs_x = 2, .ofs_y = 0},
    {.bitmap_index = 2175, .adv_w = 310, .box_w = 16, .box_h = 29, .ofs_x = 2, .ofs_y = 0},
    {.bitmap_index = 2233, .adv_w = 395, .box_w = 21, .box_h = 29, .ofs_x = 2, .ofs_y = 0},
    {.bitmap_index = 2310, .adv_w = 323, .box_w = 16, .box_h = 29, .ofs_x = 2, .ofs_y = 0},
    {.bitmap_index = 2368, .adv_w = 317, .box_w = 16, .box_h = 29, .ofs_x = 2, .ofs_y = 0},
    {.bitmap_index = 2426, .adv_w = 311, .box_w = 16, .box_h = 29, .ofs_x = 2, .ofs_y = 0},
    {.bitmap_index = 2484, .adv_w = 316, .box_w = 16, .box_h = 33, .ofs_x = 2, .ofs_y = -4},
    {.bitmap_index = 2550, .adv_w = 310, .box_w = 16, .box_h = 29, .ofs_x = 2, .ofs_y = 0},
    {.bitmap_index = 2608, .adv_w = 317, .box_w = 16, .box_h = 30, .ofs_x = 2, .ofs_y = 0},
    {.bitmap_index = 2668, .adv_w = 241, .box_w = 16, .box_h = 29, .ofs_x = 0, .ofs_y = 0},
    {.bitmap_index = 2726, .adv_w = 317, .box_w = 16, .box_h = 29, .ofs_x = 2, .ofs_y = 0},
    {.bitmap_index = 2784, .adv_w = 301, .box_w = 19, .box_h = 29, .ofs_x = 0, .ofs_y = 0},
    {.bitmap_index = 2853, .adv_w = 369, .box_w = 21, .box_h = 29, .ofs_x = 1, .ofs_y = 0},
    {.bitmap_index = 2930, .adv_w = 329, .box_w = 17, .box_h = 29, .ofs_x = 2, .ofs_y = 0},
    {.bitmap_index = 2992, .adv_w = 275, .box_w = 18, .box_h = 29, .ofs_x = 0, .ofs_y = 0},
    {.bitmap_index = 3058, .adv_w = 318, .box_w = 16, .box_h = 29, .ofs_x = 2, .ofs_y = 0},
    {.bitmap_index = 3116, .adv_w = 182, .box_w = 9, .box_h = 37, .ofs_x = 2, .ofs_y = -4},
    {.bitmap_index = 3158, .adv_w = 198, .box_w = 9, .box_h = 38, .ofs_x = 1, .ofs_y = -4},
    {.bitmap_index = 3201, .adv_w = 182, .box_w = 9, .box_h = 37, .ofs_x = 1, .ofs_y = -4},
    {.bitmap_index = 3243, .adv_w = 340, .box_w = 18, .box_h = 15, .ofs_x = 2, .ofs_y = 13},
    {.bitmap_index = 3277, .adv_w = 326, .box_w = 18, .box_h = 3, .ofs_x = 1, .ofs_y = 3},
    {.bitmap_index = 3284, .adv_w = 84, .box_w = 6, .box_h = 6, .ofs_x = 0, .ofs_y = 28},
    {.bitmap_index = 3289, .adv_w = 280, .box_w = 13, .box_h = 20, .ofs_x = 2, .ofs_y = 0},
    {.bitmap_index = 3322, .adv_w = 272, .box_w = 13, .box_h = 29, .ofs_x = 2, .ofs_y = 0},
    {.bitmap_index = 3370, .adv_w = 259, .box_w = 13, .box_h = 20, .ofs_x = 2, .ofs_y = 0},
    {.bitmap_index = 3403, .adv_w = 272, .box_w = 13, .box_h = 29, .ofs_x = 2, .ofs_y = 0},
    {.bitmap_index = 3451, .adv_w = 272, .box_w = 13, .box_h = 20, .ofs_x = 2, .ofs_y = 0},
    {.bitmap_index = 3484, .adv_w = 194, .box_w = 10, .box_h = 29, .ofs_x = 1, .ofs_y = 0},
    {.bitmap_index = 3521, .adv_w = 279, .box_w = 13, .box_h = 24, .ofs_x = 2, .ofs_y = -4},
    {.bitmap_index = 3560, .adv_w = 278, .box_w = 13, .box_h = 29, .ofs_x = 2, .ofs_y = 0},
    {.bitmap_index = 3608, .adv_w = 136, .box_w = 4, .box_h = 27, .ofs_x = 2, .ofs_y = 0},
    {.bitmap_index = 3622, .adv_w = 134, .box_w = 7, .box_h = 30, .ofs_x = -1, .ofs_y = -4},
    {.bitmap_index = 3649, .adv_w = 232, .box_w = 12, .box_h = 29, .ofs_x = 2, .ofs_y = 0},
    {.bitmap_index = 3693, .adv_w = 122, .box_w = 4, .box_h = 29, .ofs_x = 2, .ofs_y = 0},
    {.bitmap_index = 3708, .adv_w = 379, .box_w = 19, .box_h = 20, .ofs_x = 2, .ofs_y = 0},
    {.bitmap_index = 3756, .adv_w = 286, .box_w = 13, .box_h = 20, .ofs_x = 2, .ofs_y = 0},
    {.bitmap_index = 3789, .adv_w = 273, .box_w = 13, .box_h = 20, .ofs_x = 2, .ofs_y = 0},
    {.bitmap_index = 3822, .adv_w = 278, .box_w = 13, .box_h = 24, .ofs_x = 2, .ofs_y = -4},
    {.bitmap_index = 3861, .adv_w = 278, .box_w = 13, .box_h = 24, .ofs_x = 2, .ofs_y = -4},
    {.bitmap_index = 3900, .adv_w = 147, .box_w = 7, .box_h = 20, .ofs_x = 2, .ofs_y = 0},
    {.bitmap_index = 3918, .adv_w = 273, .box_w = 13, .box_h = 20, .ofs_x = 2, .ofs_y = 0},
    {.bitmap_index = 3951, .adv_w = 218, .box_w = 12, .box_h = 25, .ofs_x = 1, .ofs_y = 0},
    {.bitmap_index = 3989, .adv_w = 285, .box_w = 13, .box_h = 20, .ofs_x = 2, .ofs_y = 0},
    {.bitmap_index = 4022, .adv_w = 238, .box_w = 12, .box_h = 20, .ofs_x = 1, .ofs_y = 0},
    {.bitmap_index = 4052, .adv_w = 387, .box_w = 22, .box_h = 20, .ofs_x = 1, .ofs_y = 0},
    {.bitmap_index = 4107, .adv_w = 228, .box_w = 13, .box_h = 20, .ofs_x = 1, .ofs_y = 0},
    {.bitmap_index = 4140, .adv_w = 266, .box_w = 13, .box_h = 24, .ofs_x = 2, .ofs_y = -4},
    {.bitmap_index = 4179, .adv_w = 246, .box_w = 13, .box_h = 20, .ofs_x = 1, .ofs_y = 0},
    {.bitmap_index = 4212, .adv_w = 173, .box_w = 9, .box_h = 36, .ofs_x = 2, .ofs_y = -4},
    {.bitmap_index = 4253, .adv_w = 124, .box_w = 4, .box_h = 37, .ofs_x = 2, .ofs_y = -4},
    {.bitmap_index = 4272, .adv_w = 175, .box_w = 9, .box_h = 37, .ofs_x = 1, .ofs_y = -4},
    {.bitmap_index = 4314, .adv_w = 275, .box_w = 15, .box_h = 8, .ofs_x = 1, .ofs_y = 13}
};

/*---------------------
 *  CHARACTER MAPPING
 *--------------------*/



/*Collect the unicode lists and glyph_id offsets*/
static const lv_font_fmt_txt_cmap_t cmaps[] =
{
    {
        .range_start = 32, .range_length = 95, .glyph_id_start = 1,
        .unicode_list = NULL, .glyph_id_ofs_list = NULL, .list_length = 0, .type = LV_FONT_FMT_TXT_CMAP_FORMAT0_TINY
    }
};



/*--------------------
 *  ALL CUSTOM DATA
 *--------------------*/

#if LV_VERSION_CHECK(8, 0, 0)
/*Store all the custom data of the font*/
static  lv_font_fmt_txt_glyph_cache_t cache;
static const lv_font_fmt_txt_dsc_t font_dsc = {
#else
static lv_font_fmt_txt_dsc_t font_dsc = {
#endif
    .glyph_bitmap = glyph_bitmap,
    .glyph_dsc = glyph_dsc,
    .cmaps = cmaps,
    .kern_dsc = NULL,
    .kern_scale = 0,
    .cmap_num = 1,
    .bpp = 1,
    .kern_classes = 0,
    .bitmap_format = 0,
#if LV_VERSION_CHECK(8, 0, 0)
    .cache = &cache
#endif
};


/*-----------------
 *  PUBLIC FONT
 *----------------*/

/*Initialize a public general font descriptor*/
#if LV_VERSION_CHECK(8, 0, 0)
const lv_font_t digital_medium = {
#else
lv_font_t digital_medium = {
#endif
    .get_glyph_dsc = lv_font_get_glyph_dsc_fmt_txt,    /*Function pointer to get glyph's data*/
    .get_glyph_bitmap = lv_font_get_bitmap_fmt_txt,    /*Function pointer to get glyph's bitmap*/
    .line_height = 38,          /*The maximum line height required by the font*/
    .base_line = 4,             /*Baseline measured from the bottom of the line*/
#if !(LVGL_VERSION_MAJOR == 6 && LVGL_VERSION_MINOR == 0)
    .subpx = LV_FONT_SUBPX_NONE,
#endif
#if LV_VERSION_CHECK(7, 4, 0)
    .underline_position = -3,
    .underline_thickness = 2,
#endif
    .dsc = &font_dsc           /*The custom font data. Will be accessed by `get_glyph_bitmap/dsc` */
};



#endif /*#if DIGITAL_MEDIUM*/
